HAASNicolas/PROJET_ELECTRONIQUE_MIDI/Software/Controller_MIDI/Core/Inc/studentwork.h

/*
 * studentwork.h
 *
 *  Created on: Mar 25, 2024
 *      Author: eleve
 */

#include <stdio.h>
#include <stdlib.h>

#ifndef INC_STUDENTWORK_H_
#define INC_STUDENTWORK_H_
#endif /* INC_STUDENTWORK_H_ */

void setup(void);
void loop(void);
